herbyderb01/BaleCounter/SquareLineUIProject/cache/thumb_408742551close.png

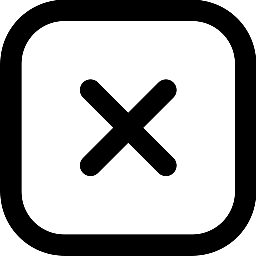
SquareLineUIProject/cache/thumb_408742551close.png
