herbyderb01/BaleCounter/SquareLineUIProject/cache/thumb_1055216652setting_big.png

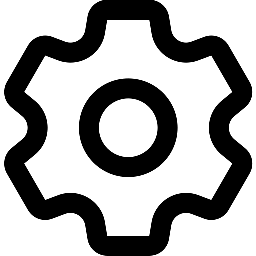
SquareLineUIProject/cache/thumb_1055216652setting_big.png
